crice009/PillDispenser.FabAcademy2017-beta/hopper node controller/hopper controller/images.toolpaths/hnctraces.png

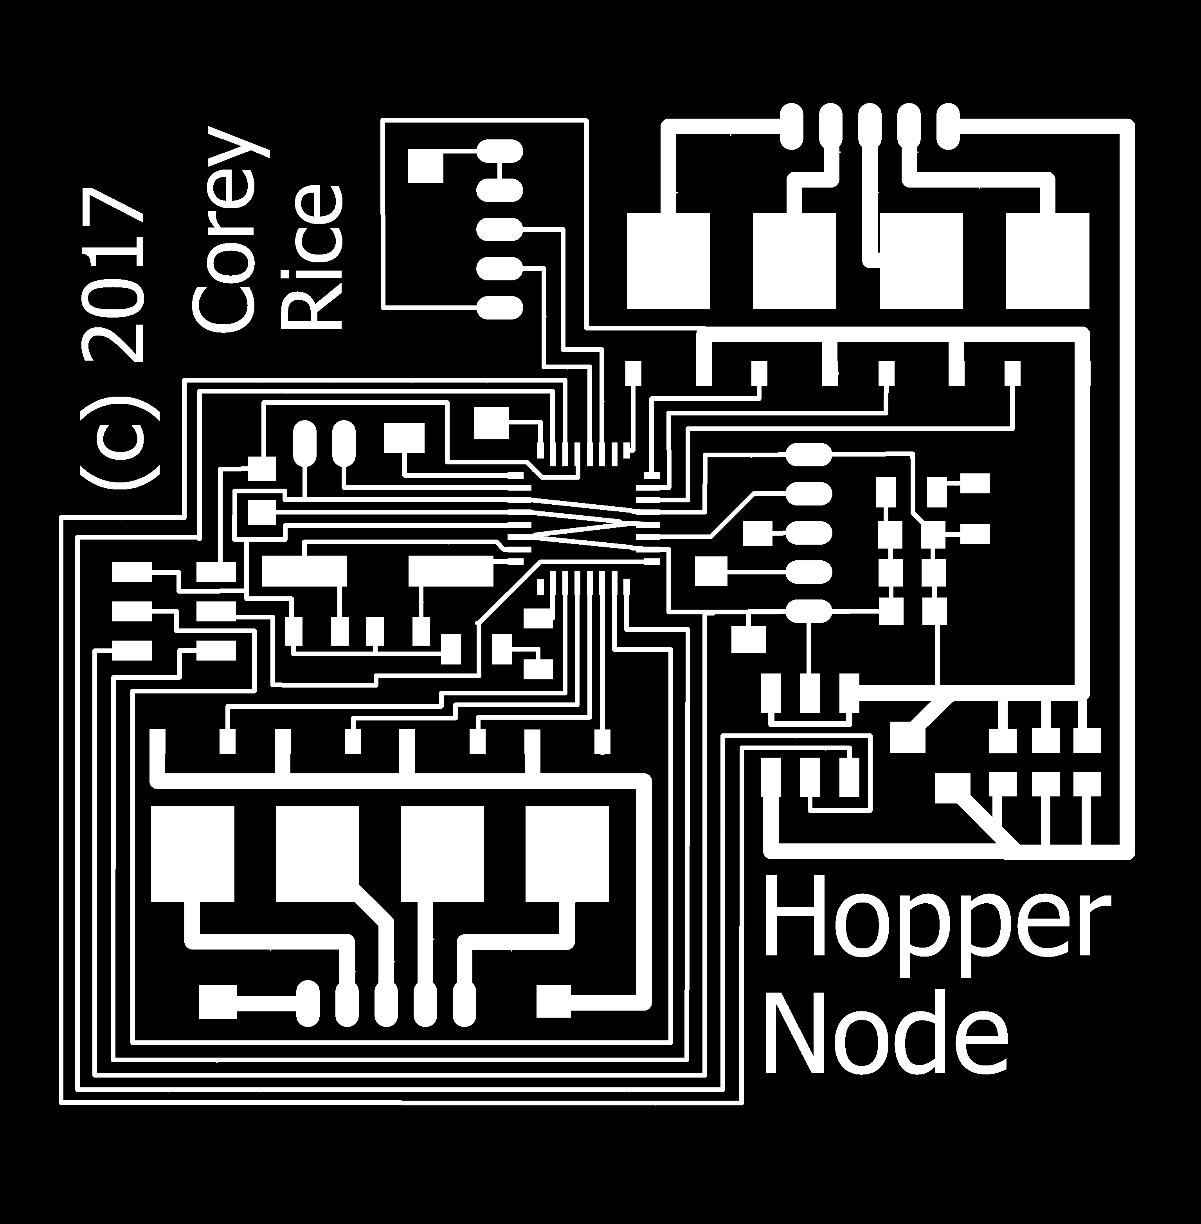
hopper node controller/hopper controller/images.toolpaths/hnctraces.png
