crice009/PillDispenser.FabAcademy2017-beta/hopper node controller/hopper controller/images.toolpaths/hoppernodecontroller.png

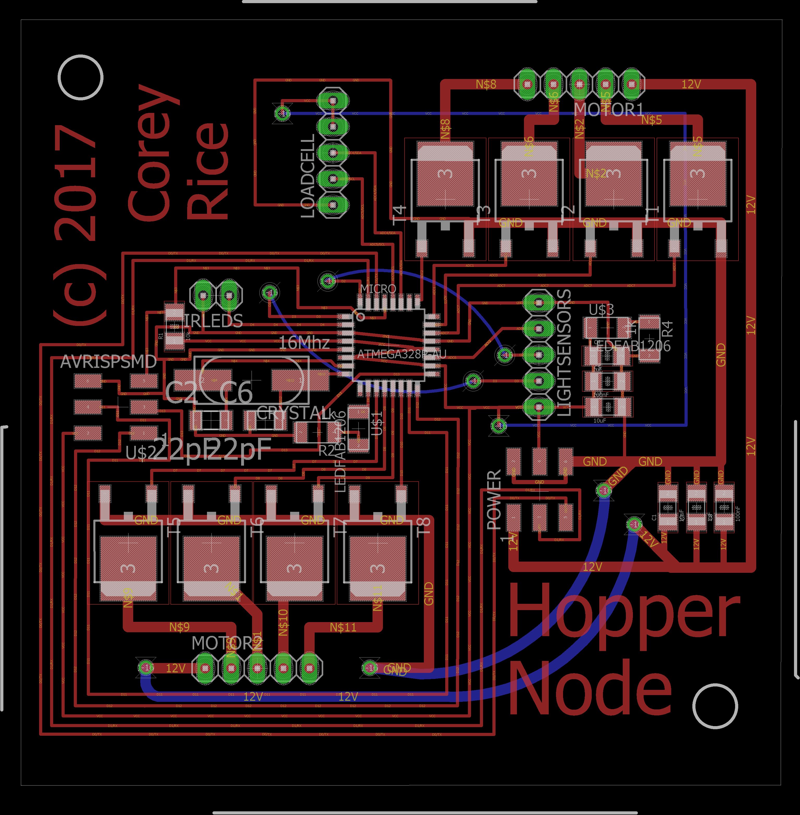
hopper node controller/hopper controller/images.toolpaths/hoppernodecontroller.png
