crice009/PillDispenser.FabAcademy2017-beta/hopper node controller/ir led wafer/images.toolpaths.flippedhorizontal/irledwafer.png

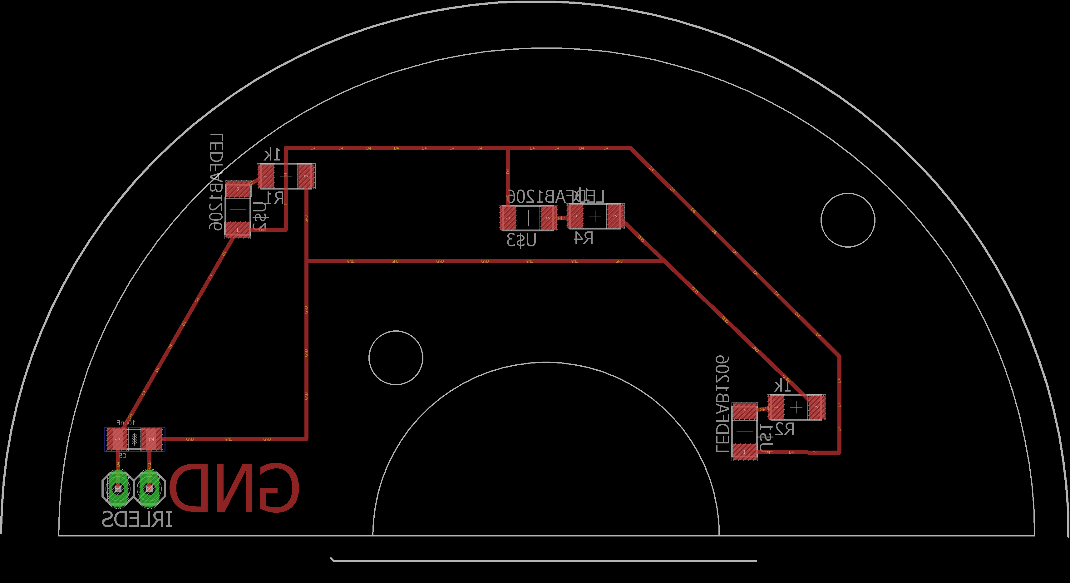
hopper node controller/ir led wafer/images.toolpaths.flippedhorizontal/irledwafer.png
