crice009/PillDispenser.FabAcademy2017-beta/hopper node controller/ir light sensor wafer/images.toolpaths/irlightsensorwafer.png

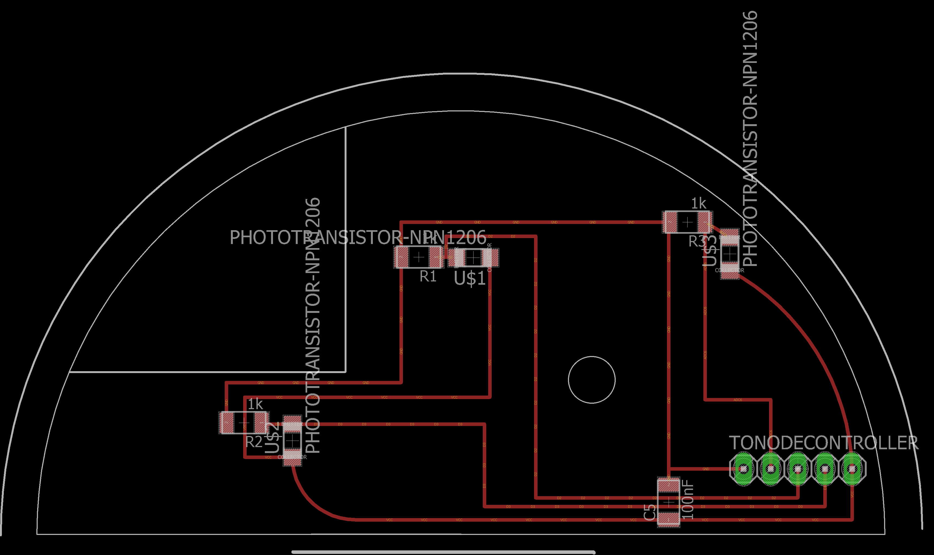
hopper node controller/ir light sensor wafer/images.toolpaths/irlightsensorwafer.png
