crice009/PillDispenser.FabAcademy2017-beta/hopper node controller/ir light sensor wafer/images.toolpaths/irlswoutline.png

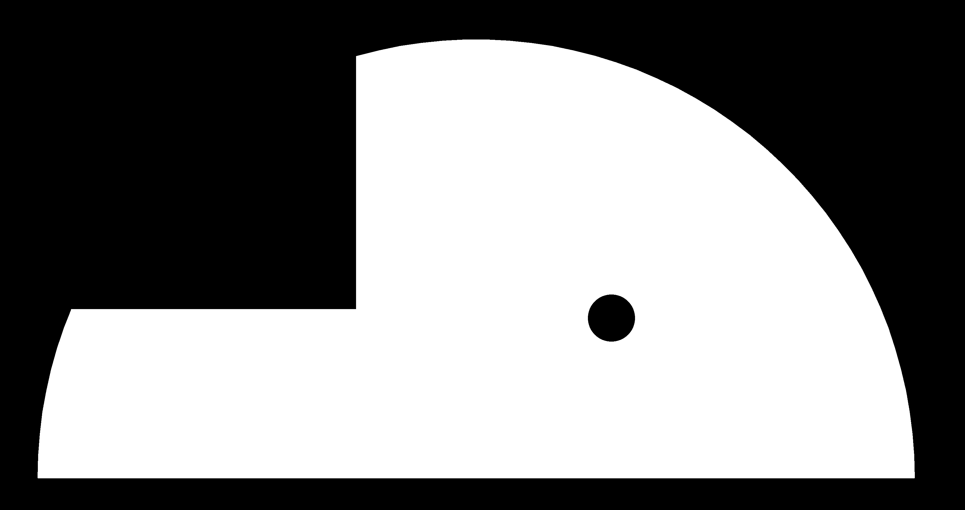
hopper node controller/ir light sensor wafer/images.toolpaths/irlswoutline.png
