crice009/PillDispenser.FabAcademy2017-beta/main hub interface/keypad connector/images.toolpaths/kcholes.png

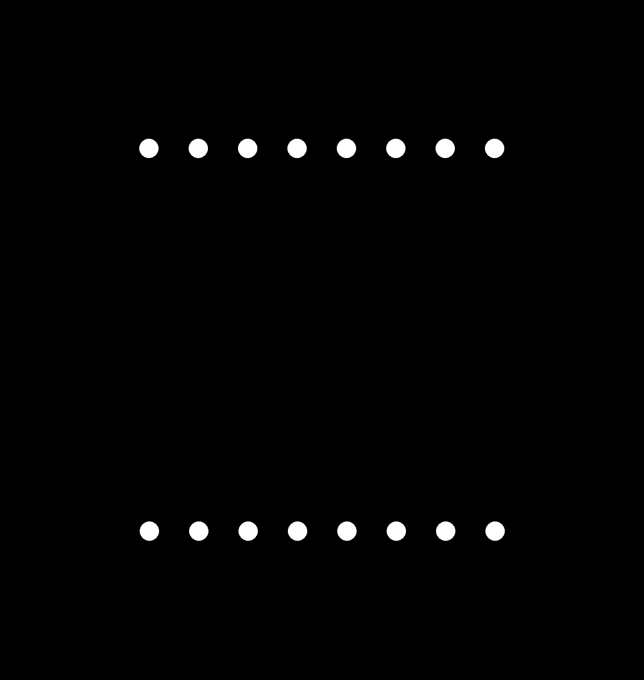
main hub interface/keypad connector/images.toolpaths/kcholes.png
