crice009/PillDispenser.FabAcademy2017-beta/main hub interface/keypad connector/images.toolpaths/kctraces.png

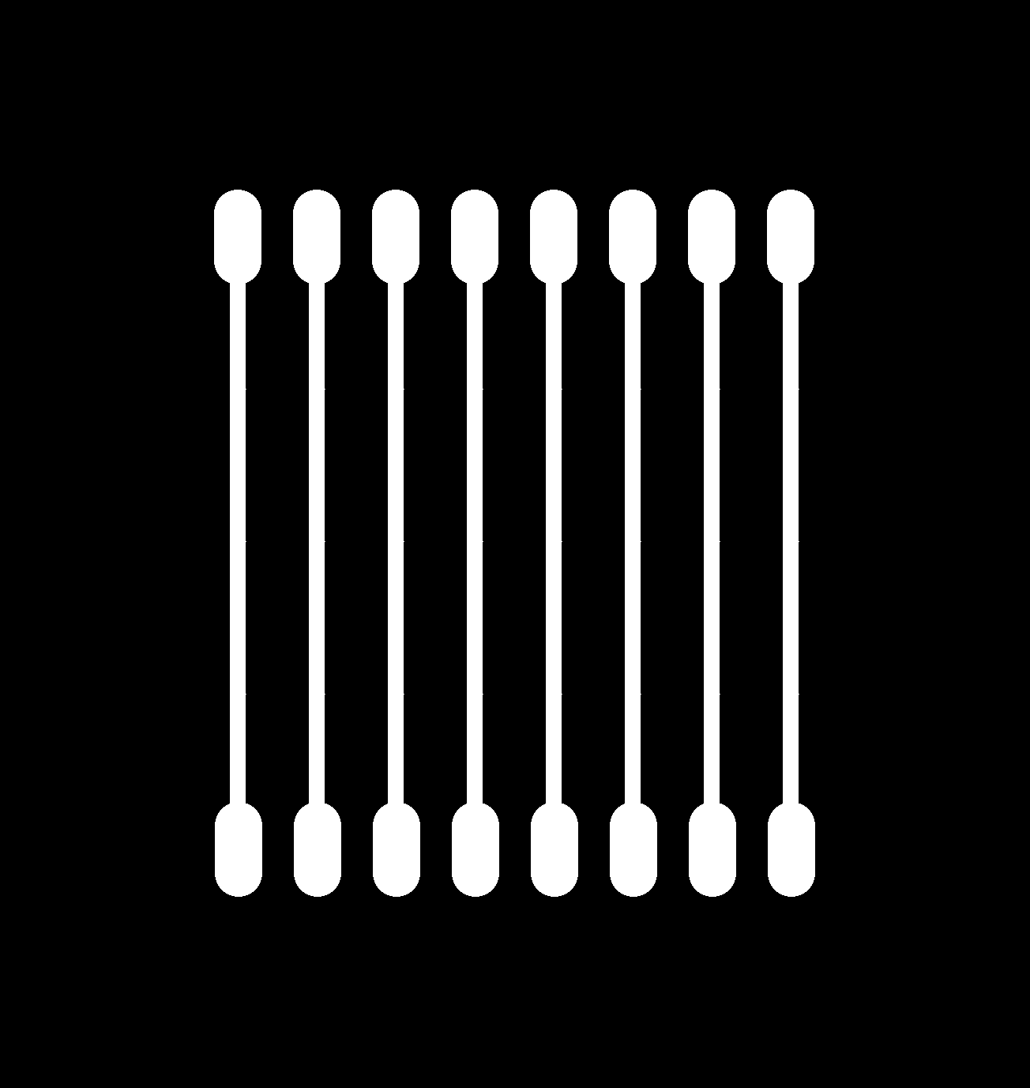
main hub interface/keypad connector/images.toolpaths/kctraces.png
