crice009/PillDispenser.FabAcademy2017-beta/main hub interface/power subpanel/images.toolpaths/psptraces.png

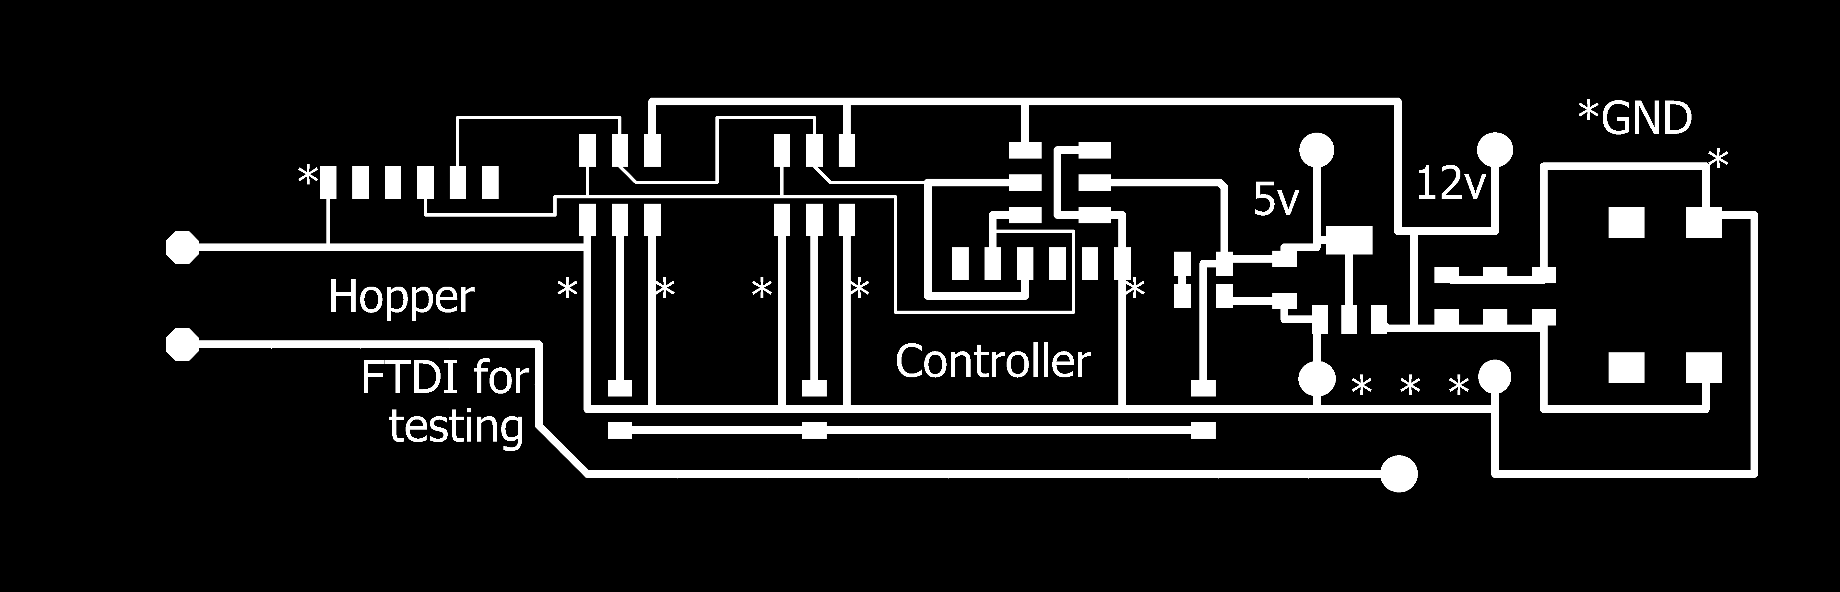
main hub interface/power subpanel/images.toolpaths/psptraces.png
